mjmilez/Garden-E-Cutters/logs/Matthew/Media/Screenshot 2026-03-03 at 1.21.23 PM.png

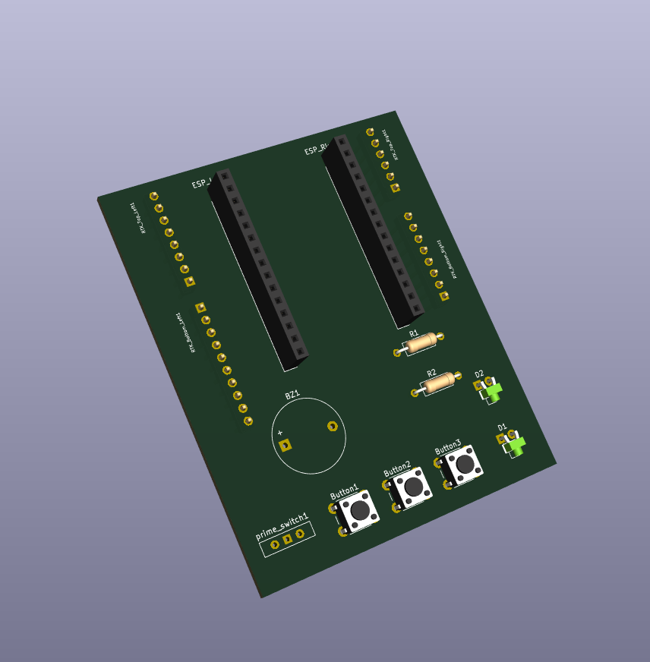
logs/Matthew/Media/Screenshot 2026-03-03 at 1.21.23 PM.png
