mjmilez/Garden-E-Cutters/logs/Alex/IMG_9044.webp

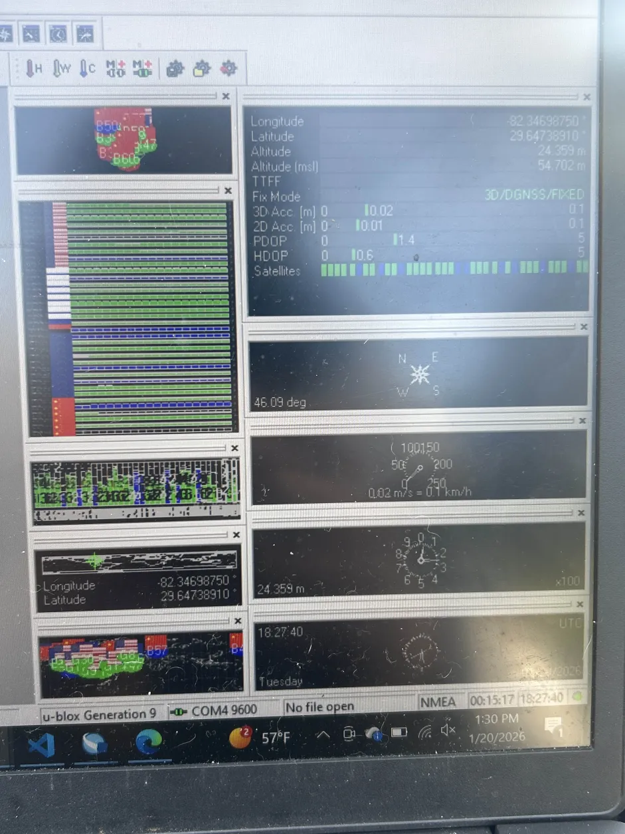
logs/Alex/IMG_9044.webp
