mjmilez/Garden-E-Cutters/logs/Matthew/Media/Screenshot 2026-03-05 at 5.34.50 PM.png

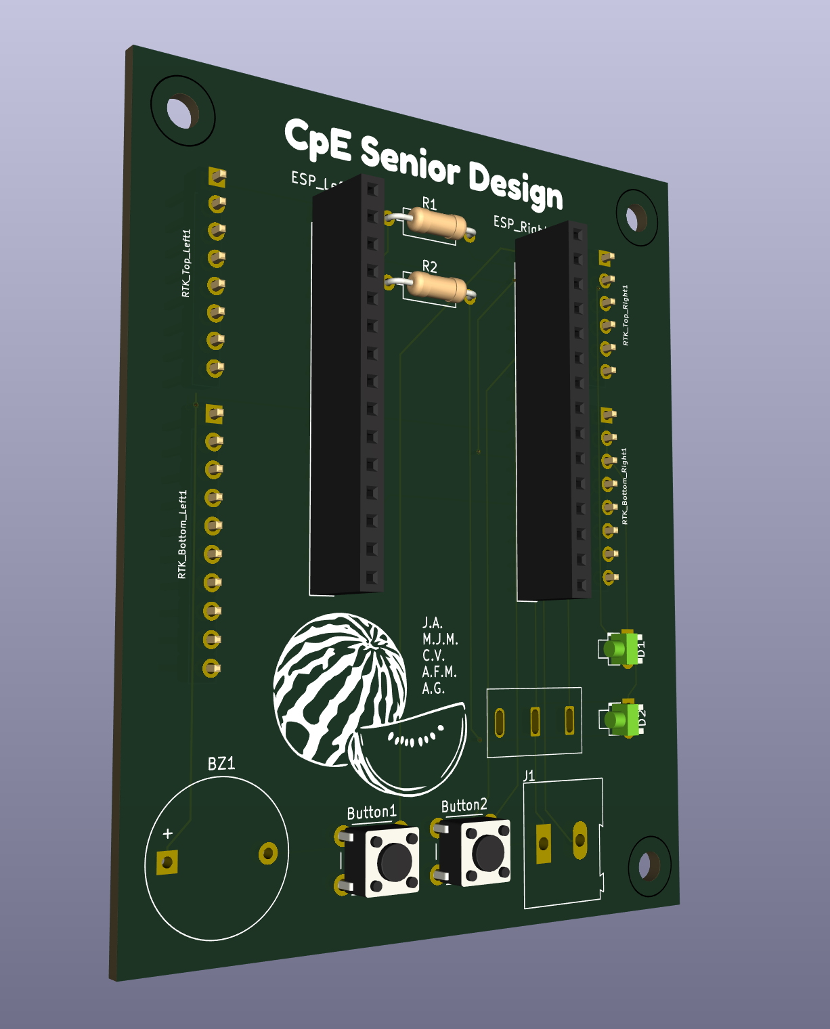
logs/Matthew/Media/Screenshot 2026-03-05 at 5.34.50 PM.png
