mjmilez/Garden-E-Cutters/shears-fw/main/log_transfer_server.c

/*
 * log_transfer_server.c
 *
 * Shears-side GATT server for BLE log transfer.
 *
 * Exposes a custom service that allows the base to request a file by name
 * and receive it as indexed chunks:
 *   - control characteristic: START_TRANSFER / ABORT writes, STATUS_* notifies
 *   - data characteristic: file chunk notifications with a chunk index
 *
 * File data is read from SPIFFS and streamed out from a background task.
 */

#include <stdio.h>
#include <string.h>

#include "freertos/FreeRTOS.h"
#include "freertos/task.h"

#include "esp_log.h"

#include "host/ble_hs.h"
#include "host/ble_att.h"

#include "log_transfer_server.h"
#include "log_transfer_protocol.h"
#include "shears_gpsStorage.h"

static const char *TAG = "log_xfer_srv";

/* UUIDs for the custom log transfer service and characteristics. */
#define LOG_SVC_UUID       0xFFF0
#define LOG_CTRL_CHR_UUID  0xFFF1
#define LOG_DATA_CHR_UUID  0xFFF2

#define LOG_TRANSFER_INVALID_CONN_HANDLE BLE_HS_CONN_HANDLE_NONE

typedef struct {
	bool		active;
	char		filename[64];
	FILE		*fp;
	uint32_t	file_size;
	uint32_t	bytes_sent;
	uint16_t	chunk_index;
	uint16_t	chunk_size;
	uint16_t	conn_handle;
	uint16_t	ctrl_val_handle;
	uint16_t	data_val_handle;
} log_transfer_t;

static log_transfer_t g_log_xfer;

static uint16_t g_ctrl_char_handle = 0;
static uint16_t g_data_char_handle = 0;

static int	log_ctrl_access_cb(uint16_t conn_handle,
				   uint16_t attr_handle,
				   struct ble_gatt_access_ctxt *ctxt,
				   void *arg);
static int	log_data_access_cb(uint16_t conn_handle,
				   uint16_t attr_handle,
				   struct ble_gatt_access_ctxt *ctxt,
				   void *arg);
static void	log_transfer_task(void *arg);
static bool	start_transfer_internal(uint16_t conn_handle,
					const uint8_t *filename_buf,
					uint16_t filename_len);
static void	handle_abort_transfer(void);
static void	send_status(ctrl_status_code_t status, uint32_t file_size);

/* --- GATT service definition --------------------------------------------- */

static struct ble_gatt_svc_def log_svc_def[] = {
	{
		.type = BLE_GATT_SVC_TYPE_PRIMARY,
		.uuid = BLE_UUID16_DECLARE(LOG_SVC_UUID),
		.characteristics = (struct ble_gatt_chr_def[]) {
			{
				.uuid	   = BLE_UUID16_DECLARE(LOG_CTRL_CHR_UUID),
				.access_cb  = log_ctrl_access_cb,
				.flags	   = BLE_GATT_CHR_F_WRITE | BLE_GATT_CHR_F_NOTIFY,
				.val_handle = &g_ctrl_char_handle,
			},
			{
				.uuid	   = BLE_UUID16_DECLARE(LOG_DATA_CHR_UUID),
				.access_cb  = log_data_access_cb,
				.flags	   = BLE_GATT_CHR_F_NOTIFY,
				.val_handle = &g_data_char_handle,
			},
			{ 0 }
		},
	},
	{ 0 }
};

/* --- Status notifications ------------------------------------------------- */

static void send_status(ctrl_status_code_t status, uint32_t file_size)
{
	ESP_LOGI(TAG, "send_status: code=%u size=%u (conn=%u, ctrl=0x%04x)",
		 status,
		 file_size,
		 g_log_xfer.conn_handle,
		 g_log_xfer.ctrl_val_handle ? g_log_xfer.ctrl_val_handle
					    : g_ctrl_char_handle);

	uint8_t payload[1 + 1 + 4];
	uint16_t len = 0;

	payload[len++] = CTRL_EVT_STATUS;
	payload[len++] = (uint8_t)status;

	if (status == STATUS_OK) {
		memcpy(&payload[len], &file_size, sizeof(file_size));
		len += sizeof(file_size);
	}

	if (g_log_xfer.ctrl_val_handle == 0) {
		g_log_xfer.ctrl_val_handle = g_ctrl_char_handle;
	}

	if (g_log_xfer.ctrl_val_handle == 0) {
		ESP_LOGW(TAG, "send_status aborted: missing ctrl handle");
		return;
	}

	if (!log_transfer_server_isConnected()) {
		ESP_LOGW(TAG, "send_status aborted: no active connection");
		return;
	}

	struct os_mbuf *om = ble_hs_mbuf_from_flat(payload, len);
	if (!om) {
		ESP_LOGW(TAG, "send_status: allocation failed");
		return;
	}

	int rc = ble_gatts_notify_custom(g_log_xfer.conn_handle,
					 g_log_xfer.ctrl_val_handle,
					 om);
	if (rc != 0) {
		ESP_LOGW(TAG, "STATUS notify failed rc=%d", rc);
	}
}

/* --- Transfer helpers ----------------------------------------------------- */

static bool start_transfer_internal(uint16_t conn_handle,
				    const uint8_t *filename_buf,
				    uint16_t filename_len)
{
	g_log_xfer.conn_handle = conn_handle;

	/*
	 * ATT MTU includes the ATT header.
	 * Reserve 2 bytes in the payload for the chunk index.
	 */
	uint16_t mtu = ble_att_mtu(conn_handle);
	uint16_t maxNotif = (mtu > 3) ? (mtu - 3) : 0;
	uint16_t maxPayload = (maxNotif > 2) ? (maxNotif - 2) : 0;

	if (maxPayload == 0) {
		send_status(STATUS_ERR_FS, 0);
		if (g_log_xfer.fp) {
			fclose(g_log_xfer.fp);
			g_log_xfer.fp = NULL;
		}
		return false;
	}

	if (maxPayload > 160) {
		maxPayload = 160;
	}

	g_log_xfer.chunk_size = maxPayload;

	ESP_LOGI(TAG, "Using chunk_size=%u (mtu=%u, maxNotif=%u)",
		 g_log_xfer.chunk_size, mtu, maxNotif);

	if (g_log_xfer.ctrl_val_handle == 0) {
		g_log_xfer.ctrl_val_handle = g_ctrl_char_handle;
	}
	if (g_log_xfer.data_val_handle == 0) {
		g_log_xfer.data_val_handle = g_data_char_handle;
	}

	if (g_log_xfer.active) {
		send_status(STATUS_ERR_BUSY, 0);
		return false;
	}

	if (filename_len == 0 || filename_len > 48) {
		send_status(STATUS_ERR_FS, 0);
		return false;
	}

	char basename[49];
	memcpy(basename, filename_buf, filename_len);
	basename[filename_len] = '\0';

	int n = snprintf(g_log_xfer.filename,
			 sizeof(g_log_xfer.filename),
			 "/spiffs/%s",
			 basename);
	if (n <= 0 || n >= (int)sizeof(g_log_xfer.filename)) {
		send_status(STATUS_ERR_FS, 0);
		return false;
	}

	ESP_LOGI(TAG, "Start transfer for file '%s'", g_log_xfer.filename);

	FILE *fp = fopen(g_log_xfer.filename, "rb");
	if (!fp) {
		ESP_LOGW(TAG, "File not found");
		send_status(STATUS_ERR_NO_FILE, 0);
		return false;
	}

	if (fseek(fp, 0, SEEK_END) != 0) {
		fclose(fp);
		send_status(STATUS_ERR_FS, 0);
		return false;
	}

	long size = ftell(fp);
	if (size < 0) {
		fclose(fp);
		send_status(STATUS_ERR_FS, 0);
		return false;
	}

	if (fseek(fp, 0, SEEK_SET) != 0) {
		fclose(fp);
		send_status(STATUS_ERR_FS, 0);
		return false;
	}

	g_log_xfer.active	 = true;
	g_log_xfer.fp		 = fp;
	g_log_xfer.file_size	 = (uint32_t)size;
	g_log_xfer.bytes_sent	 = 0;
	g_log_xfer.chunk_index	 = 0;

	send_status(STATUS_OK, g_log_xfer.file_size);
	return true;
}

static void handle_abort_transfer(void)
{
	if (!g_log_xfer.active) {
		return;
	}

	if (g_log_xfer.fp) {
		fclose(g_log_xfer.fp);
		g_log_xfer.fp = NULL;
	}

	g_log_xfer.active = false;
	send_status(STATUS_TRANSFER_ABORTED, g_log_xfer.file_size);
}

/* --- Public API ----------------------------------------------------------- */

void log_transfer_server_setConnection(uint16_t conn_handle)
{
	g_log_xfer.conn_handle = conn_handle;
}

void log_transfer_server_clearConnection(void)
{
	g_log_xfer.conn_handle = LOG_TRANSFER_INVALID_CONN_HANDLE;
}

bool log_transfer_server_isConnected(void)
{
	return g_log_xfer.conn_handle != LOG_TRANSFER_INVALID_CONN_HANDLE;
}

bool log_transfer_server_isTransferActive(void)
{
	return g_log_xfer.active;
}

bool log_transfer_server_startTransfer(const char *filename)
{
	if (filename == NULL) {
		ESP_LOGW(TAG, "startTransfer failed: filename is NULL");
		return false;
	}

	if (filename[0] == '\0') {
		ESP_LOGW(TAG, "startTransfer failed: filename is empty");
		return false;
	}

	if (!log_transfer_server_isConnected()) {
		ESP_LOGW(TAG, "startTransfer failed: no active BLE connection");
		return false;
	}

	return start_transfer_internal(g_log_xfer.conn_handle,
				       (const uint8_t *)filename,
				       (uint16_t)strlen(filename));
}

void log_transfer_server_abortTransfer(void)
{
	handle_abort_transfer();
}

/* --- GATT callbacks ------------------------------------------------------- */

static int log_ctrl_access_cb(uint16_t conn_handle,
			      uint16_t attr_handle,
			      struct ble_gatt_access_ctxt *ctxt,
			      void *arg)
{
	(void)attr_handle;
	(void)arg;

	if (ctxt->op != BLE_GATT_ACCESS_OP_WRITE_CHR) {
		return 0;
	}

	uint16_t len = OS_MBUF_PKTLEN(ctxt->om);
	if (len == 0) {
		return 0;
	}

	uint8_t buf[80];
	if (len > sizeof(buf)) {
		len = sizeof(buf);
	}

	os_mbuf_copydata(ctxt->om, 0, len, buf);
	uint8_t opcode = buf[0];

	switch ((ctrl_opcode_t)opcode) {
	case CTRL_CMD_START_TRANSFER:
		(void)start_transfer_internal(conn_handle, &buf[1], len - 1);
		break;

	case CTRL_CMD_ABORT:
		handle_abort_transfer();
		break;

	default:
		ESP_LOGW(TAG, "Unknown CTRL opcode 0x%02X", opcode);
		break;
	}

	return 0;
}

static int log_data_access_cb(uint16_t conn_handle,
			      uint16_t attr_handle,
			      struct ble_gatt_access_ctxt *ctxt,
			      void *arg)
{
	(void)conn_handle;
	(void)attr_handle;
	(void)ctxt;
	(void)arg;

	return 0;
}

/* --- Transfer task -------------------------------------------------------- */

static void log_transfer_task(void *arg)
{
	(void)arg;

	uint8_t buf[2 + 160];

	while (1) {
		if (g_log_xfer.active && g_log_xfer.fp) {
			size_t n = fread(&buf[2], 1,
					 g_log_xfer.chunk_size,
					 g_log_xfer.fp);

			ESP_LOGI(TAG, "read: chunk=%u n=%u sent=%u/%u (chunk_size=%u)",
				 g_log_xfer.chunk_index,
				 (unsigned)n,
				 g_log_xfer.bytes_sent,
				 g_log_xfer.file_size,
				 g_log_xfer.chunk_size);

			if (n > 0) {
				ESP_LOGI(TAG, "head: %02X %02X %02X %02X  %02X %02X %02X %02X",
					 buf[2],
					 (n > 1) ? buf[3] : 0,
					 (n > 2) ? buf[4] : 0,
					 (n > 3) ? buf[5] : 0,
					 (n > 4) ? buf[6] : 0,
					 (n > 5) ? buf[7] : 0,
					 (n > 6) ? buf[8] : 0,
					 (n > 7) ? buf[9] : 0);
			}

			if (n > 0 && g_log_xfer.data_val_handle != 0 && log_transfer_server_isConnected()) {
				uint16_t idx = g_log_xfer.chunk_index;
				memcpy(&buf[0], &idx, sizeof(idx));

				struct os_mbuf *om =
					ble_hs_mbuf_from_flat(buf, 2 + n);
				if (om) {
					int rc = ble_gatts_notify_custom(
						g_log_xfer.conn_handle,
						g_log_xfer.data_val_handle,
						om);

					ESP_LOGI(TAG, "notify: chunk=%u rc=%d bytes=%u",
						 g_log_xfer.chunk_index, rc, (unsigned)n);

					if (rc != 0) {
						ESP_LOGW(TAG, "DATA notify failed rc=%d", rc);
					}
				} else {
					ESP_LOGW(TAG, "notify: mbuf alloc failed (chunk=%u bytes=%u)",
						 g_log_xfer.chunk_index, (unsigned)n);
				}

				g_log_xfer.bytes_sent += n;
				g_log_xfer.chunk_index++;
			}

			if (n < g_log_xfer.chunk_size) {
				if (g_log_xfer.fp) {
					fclose(g_log_xfer.fp);
					g_log_xfer.fp = NULL;
				}
				g_log_xfer.active = false;

				ESP_LOGI(TAG, "done: bytes_sent=%u file_size=%u chunks=%u",
					 g_log_xfer.bytes_sent,
					 g_log_xfer.file_size,
					 g_log_xfer.chunk_index);

				send_status(STATUS_TRANSFER_DONE,
					    g_log_xfer.file_size);

				ESP_LOGI(TAG, "Clearing transferred log file '%s'",
					 g_log_xfer.filename);

				if (shearsGpsStorageClearCsv(g_log_xfer.filename)) {
					ESP_LOGI(TAG, "Cleared transferred log file");
				} else {
					ESP_LOGW(TAG, "Failed to clear transferred log file");
				}
			}

			vTaskDelay(pdMS_TO_TICKS(10));
		} else {
			vTaskDelay(pdMS_TO_TICKS(50));
		}
	}
}

/* --- Init ----------------------------------------------------------------- */

void log_transfer_server_init(void)
{
	memset(&g_log_xfer, 0, sizeof(g_log_xfer));
	g_log_xfer.conn_handle = LOG_TRANSFER_INVALID_CONN_HANDLE;

	int rc = ble_gatts_count_cfg(log_svc_def);
	if (rc != 0) {
		ESP_LOGE(TAG, "ble_gatts_count_cfg failed; rc=%d", rc);
		return;
	}

	rc = ble_gatts_add_svcs(log_svc_def);
	if (rc != 0) {
		ESP_LOGE(TAG, "ble_gatts_add_svcs failed; rc=%d", rc);
		return;
	}

	ESP_LOGI(TAG, "Log transfer service registered");

	xTaskCreate(log_transfer_task,
		    "log_xfer_task",
		    4096,
		    NULL,
		    5,
		    NULL);
}
